cad435/OpenDALI_EVG/Hardware/DALI_Load_250W_RGBW/BOM-DALI_EVG_LoadBoard(V0.1).pdf

Comment | Description | Designator | Footprint | Quantity
MOC3043 | Zero-Cross Triac Driver Output Optocoupler | A1 | DIP762W46P254L889H5 08Q6B | 1
1uF/25V | Capacitor | C1, C2, C3, C8 | C0603 | 4
10uF/25V | Capacitor | C5, C6 | C0805 | 2
ACST410-8BTR | TRIAC Alternistor -Snubberless, 600V, 4A DPAK | D1 | TO229P994X240-3N (DPAK) | 1
BZT52C15S (15V) | Zener | D4 | SOD-323 | 1
1.5A | Fuse | F1 | 1808 Fuse / FUSE_0154004 | 1
FFC 0.5mm 10Pin 90° | FFC 0.5mm 10P Bottom Connection C262659 | J1 | TE_1-1734592-0 | 1
KF142R-5.08-4P | KF142R-5.08-4P | P1 | CONN-TH_4P-P5.08_KF142R-5.08-4P | 1
KF2EDGR-3.81-5Pin | KF2EDGR-3.81-5Pin | P2 | CONN-TH_5P-P3.81_KF2EDGR-3.81-5P | 1
4 Pin male | 4 Pin male | P7 | TE_826647-4 | 1
MMBT5551 | NPN General Purpose Transistor | Q2 | SOT23 | 1
IRLU024N | N-HEXFET Power MOSFET | Q3, Q4, Q5, Q6 | TO228P680X240X837-3 (TO-251) | 4
10 | Resistor | R1, R2, R3, R7, R8, R9, R10, R17 | R0603 | 8
390 | Resistor | R4, R16 | R1206 | 2
22k | Resistor | R5 | R0603 | 1
0 | Resistor | R6 | R1206 | 1
100k | Resistor | R11, R12, R13, R14, R15 | R0603 | 5
UCC27517DBVR | 4-A/4-A single-channel gate driver with 5-V UVLO and 13-ns prop delay in SOT-23 package | U1, U2, U3, U4 | SOT23-5 | 4
