cad435/OpenDALI_EVG/Hardware/DALI_Load_250W_RGBW/DALI_EVG_LoadBoard_V0.1-Schematic.PDF

J1

P2

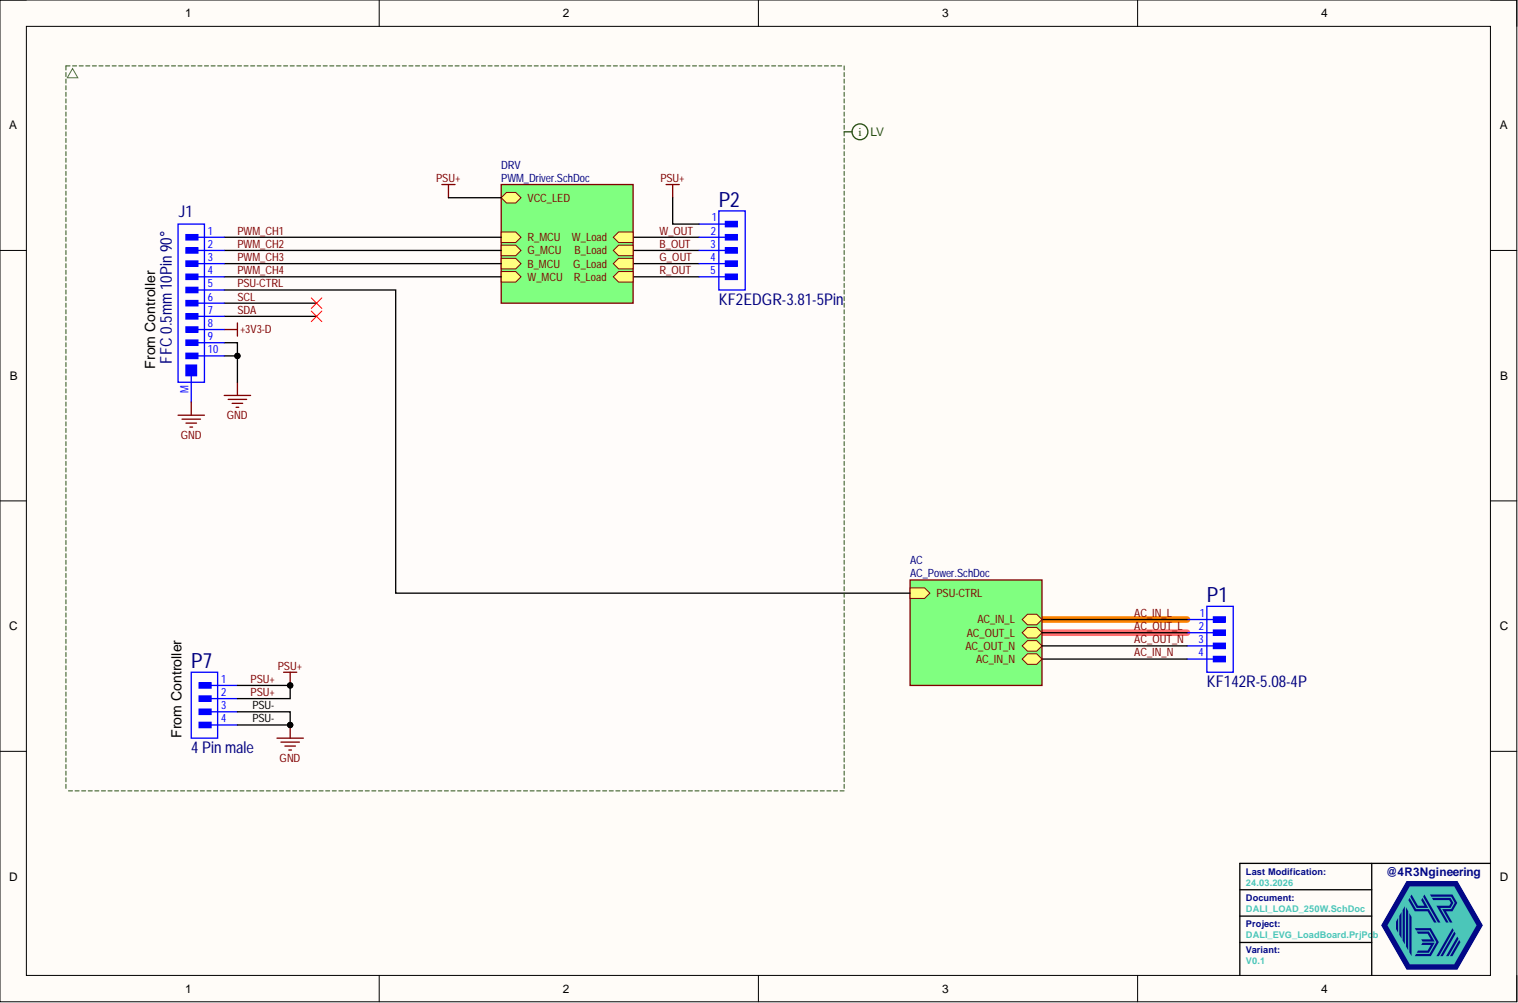
[picture p31: page 1]
st Modific; ation:; Docum; ent: DALI_LOAD_; W.SchDoc; Proje; ct: DALI_EVG; _LoadBoard.PrjPc; ariant: V0.1; PSU; 4 Pin male; R_Load; B_Load G_Load; W_Load; C_LED; V PWM_Dri; ver.SchDoc; - PSU; PWM_C; PSU-CTR; SDA +3V3-D; From Controller; AC AC_Power.SchDoc; FFC 0.5mm 10Pin 90°; KF2EDGR-3.81-5Pin

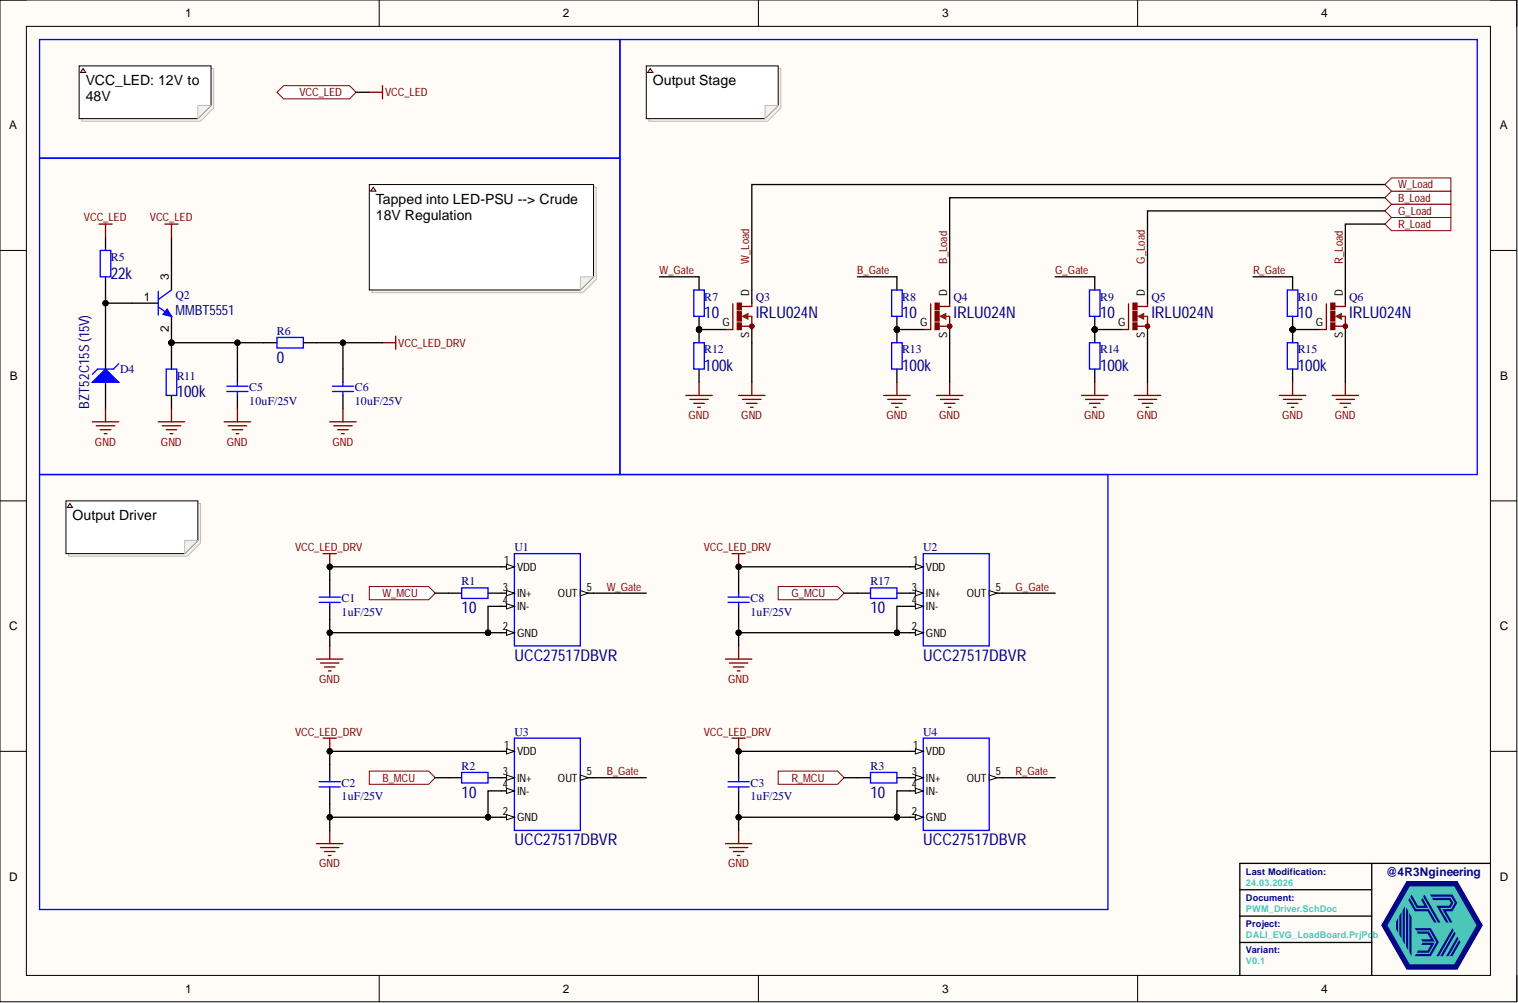
[picture p32: page 2]

Tapped into LED-PSU --> Crude
18V Regulation

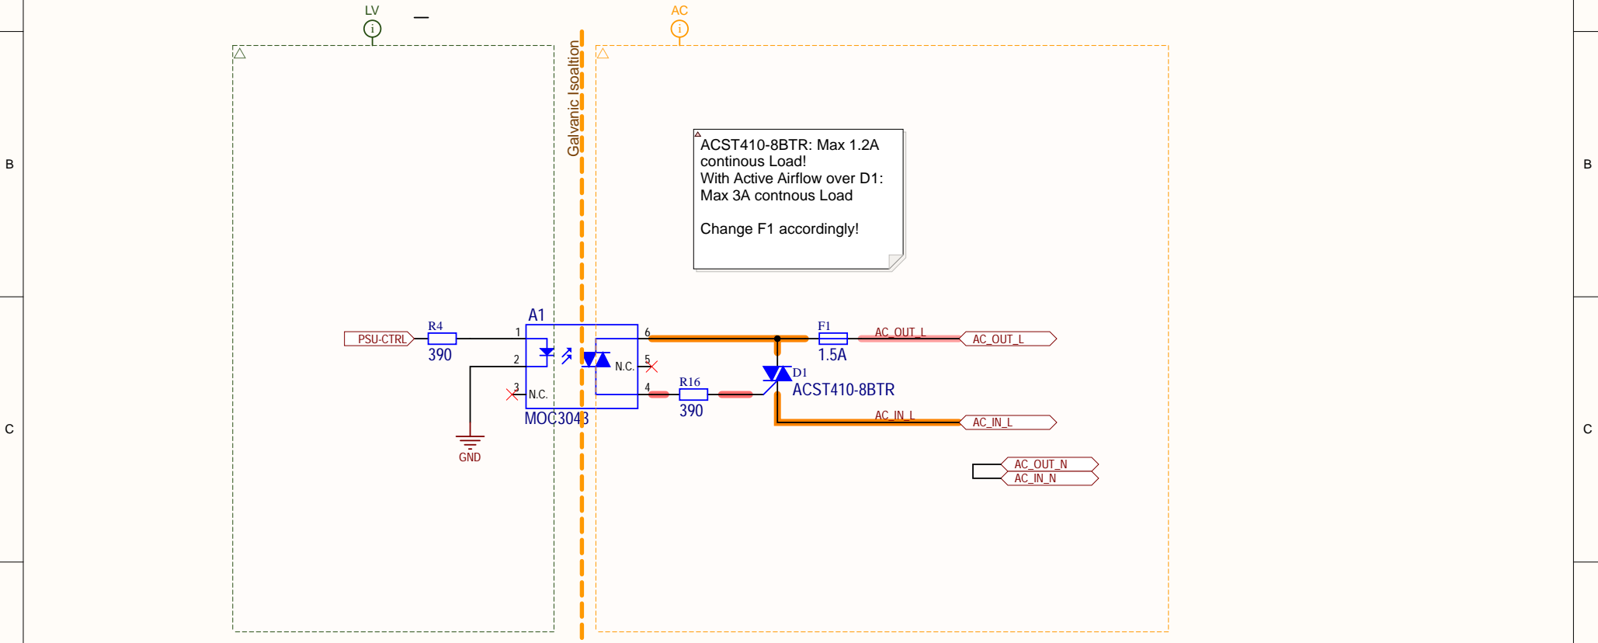
[picture p33: figure]
AC_OUT_L; AC_OUT_N AC_IN_N; MOC3043; PSU-CTRL; GND; Galvanic Isoaltion; D1 ACST410-8BTR; ACST410-8BTR: Max 1.2A continous Load! With Active Airflow over D1: Max 3A contnous Load; Change F1 accordingly!

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
D | D
A | A
Last Modification: | @4R3Ngineering 24.03.2026

Document:
AC_Power.SchDoc

Project:
DALI_EVG_LoadBoard.PrjPcb

Variant:
