cad435/OpenDALI_EVG/Hardware/DALI_Load_250W_RGBW/DALI_EVG_LoadBoard_V0.1_Assembly.PDF

A

B

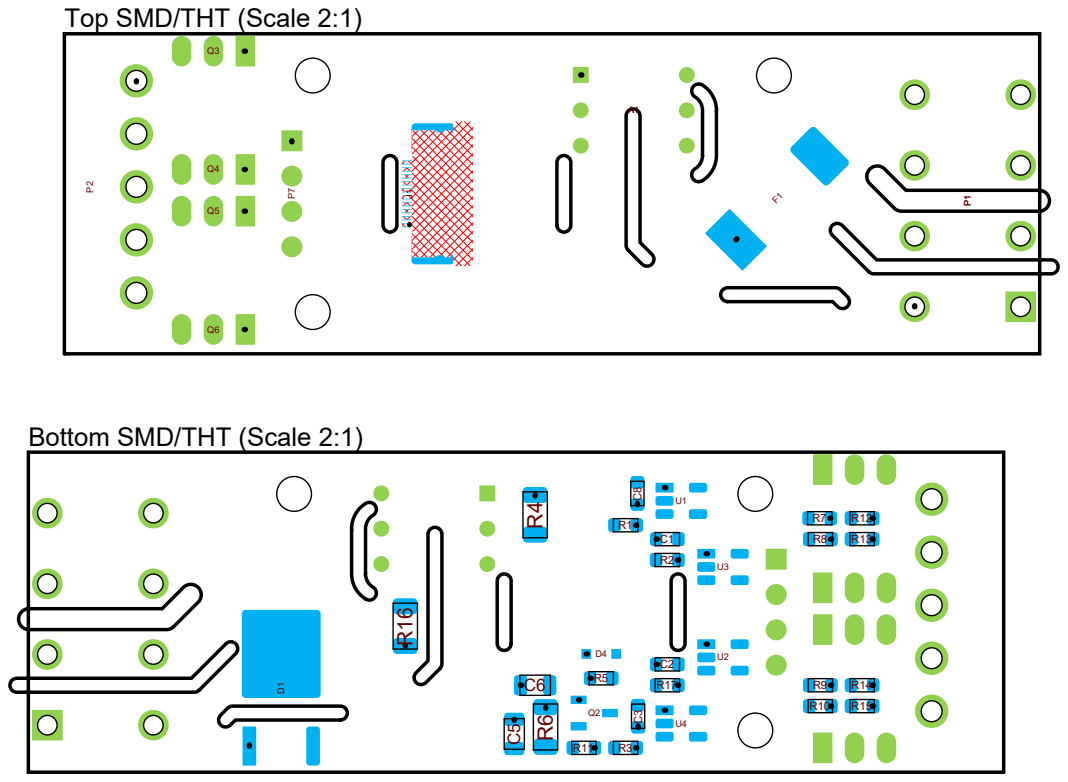
[picture p34: page 1]

Top SMD/THT (Scale 2:1) D¹

Bottom SMD/THT (Scale 2:1)

1 | 1

# Top SMD (Scale 2:1)

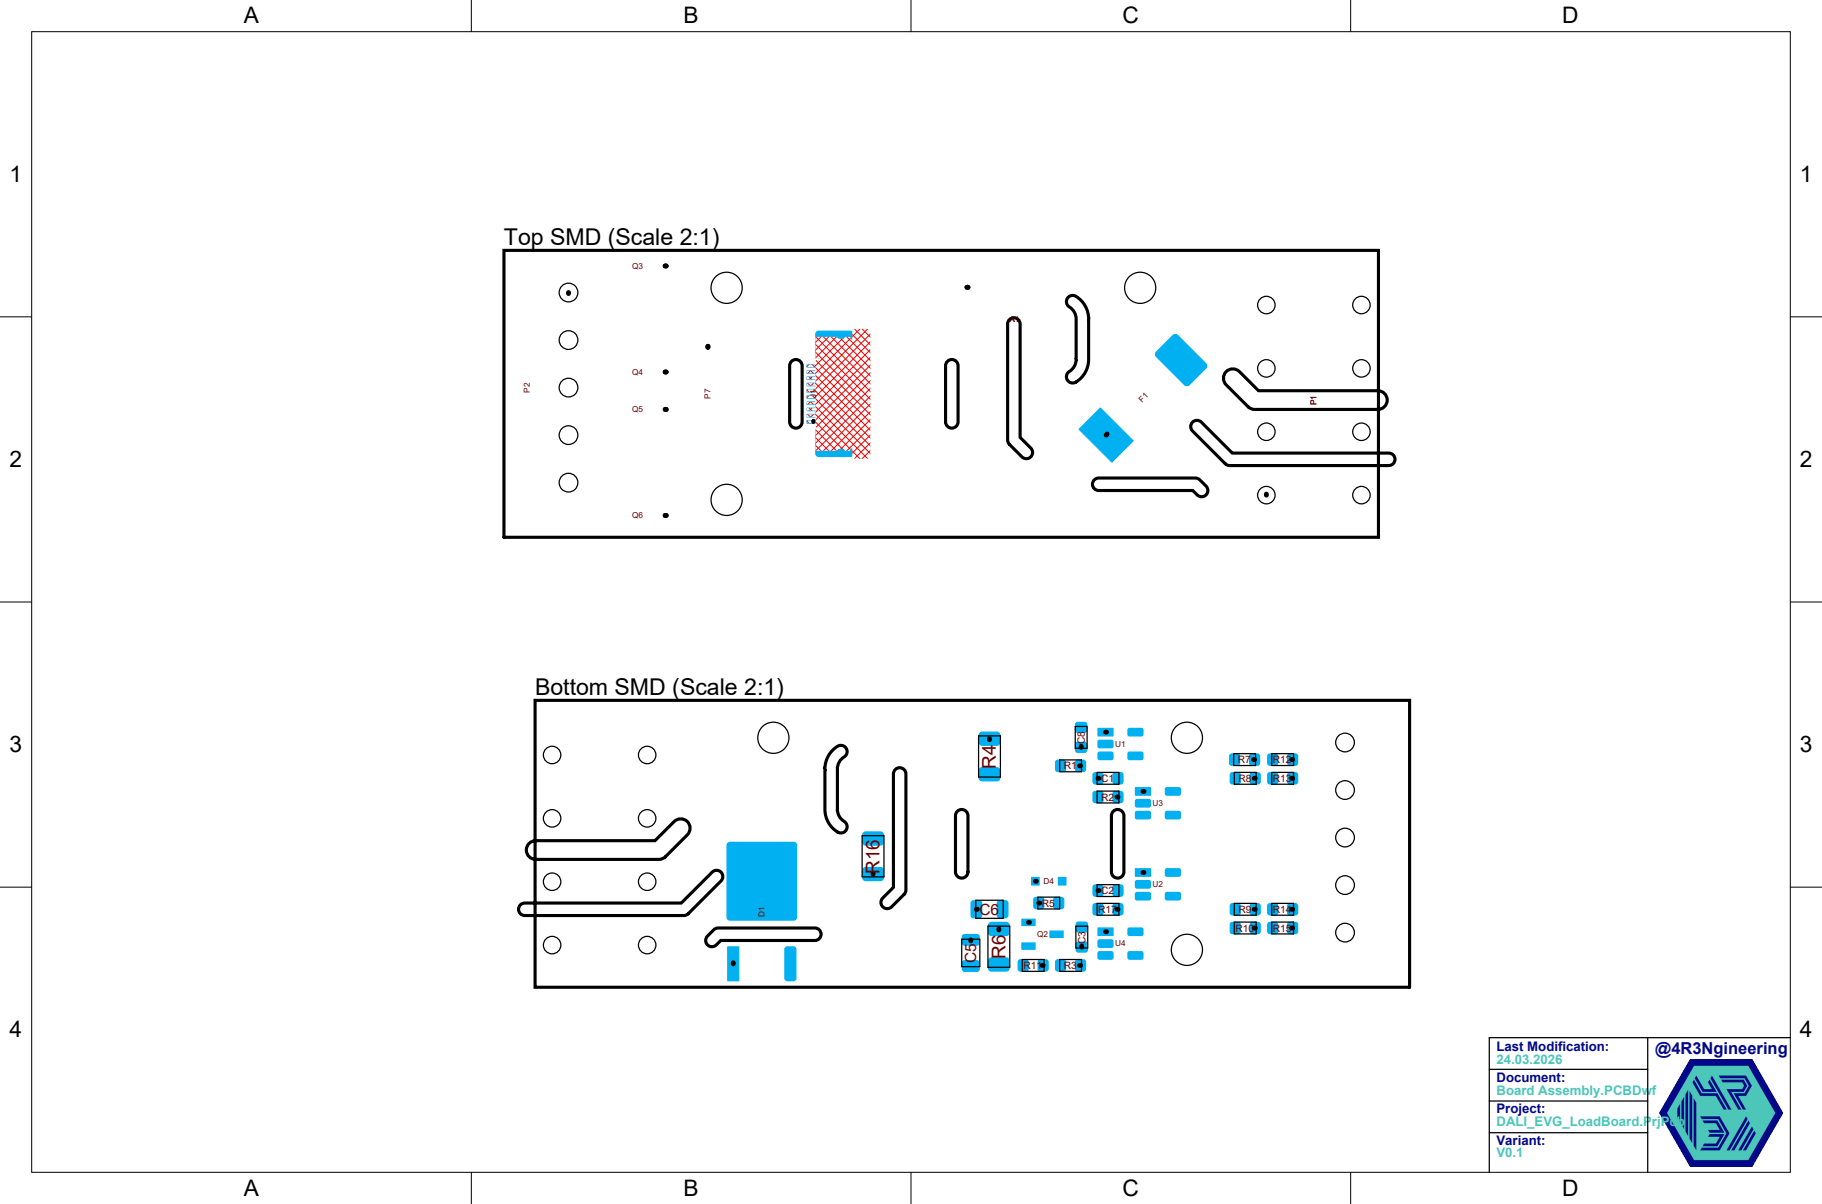
[picture p35: page 2]

1 | 1

# Top THT (Scale 2:1)

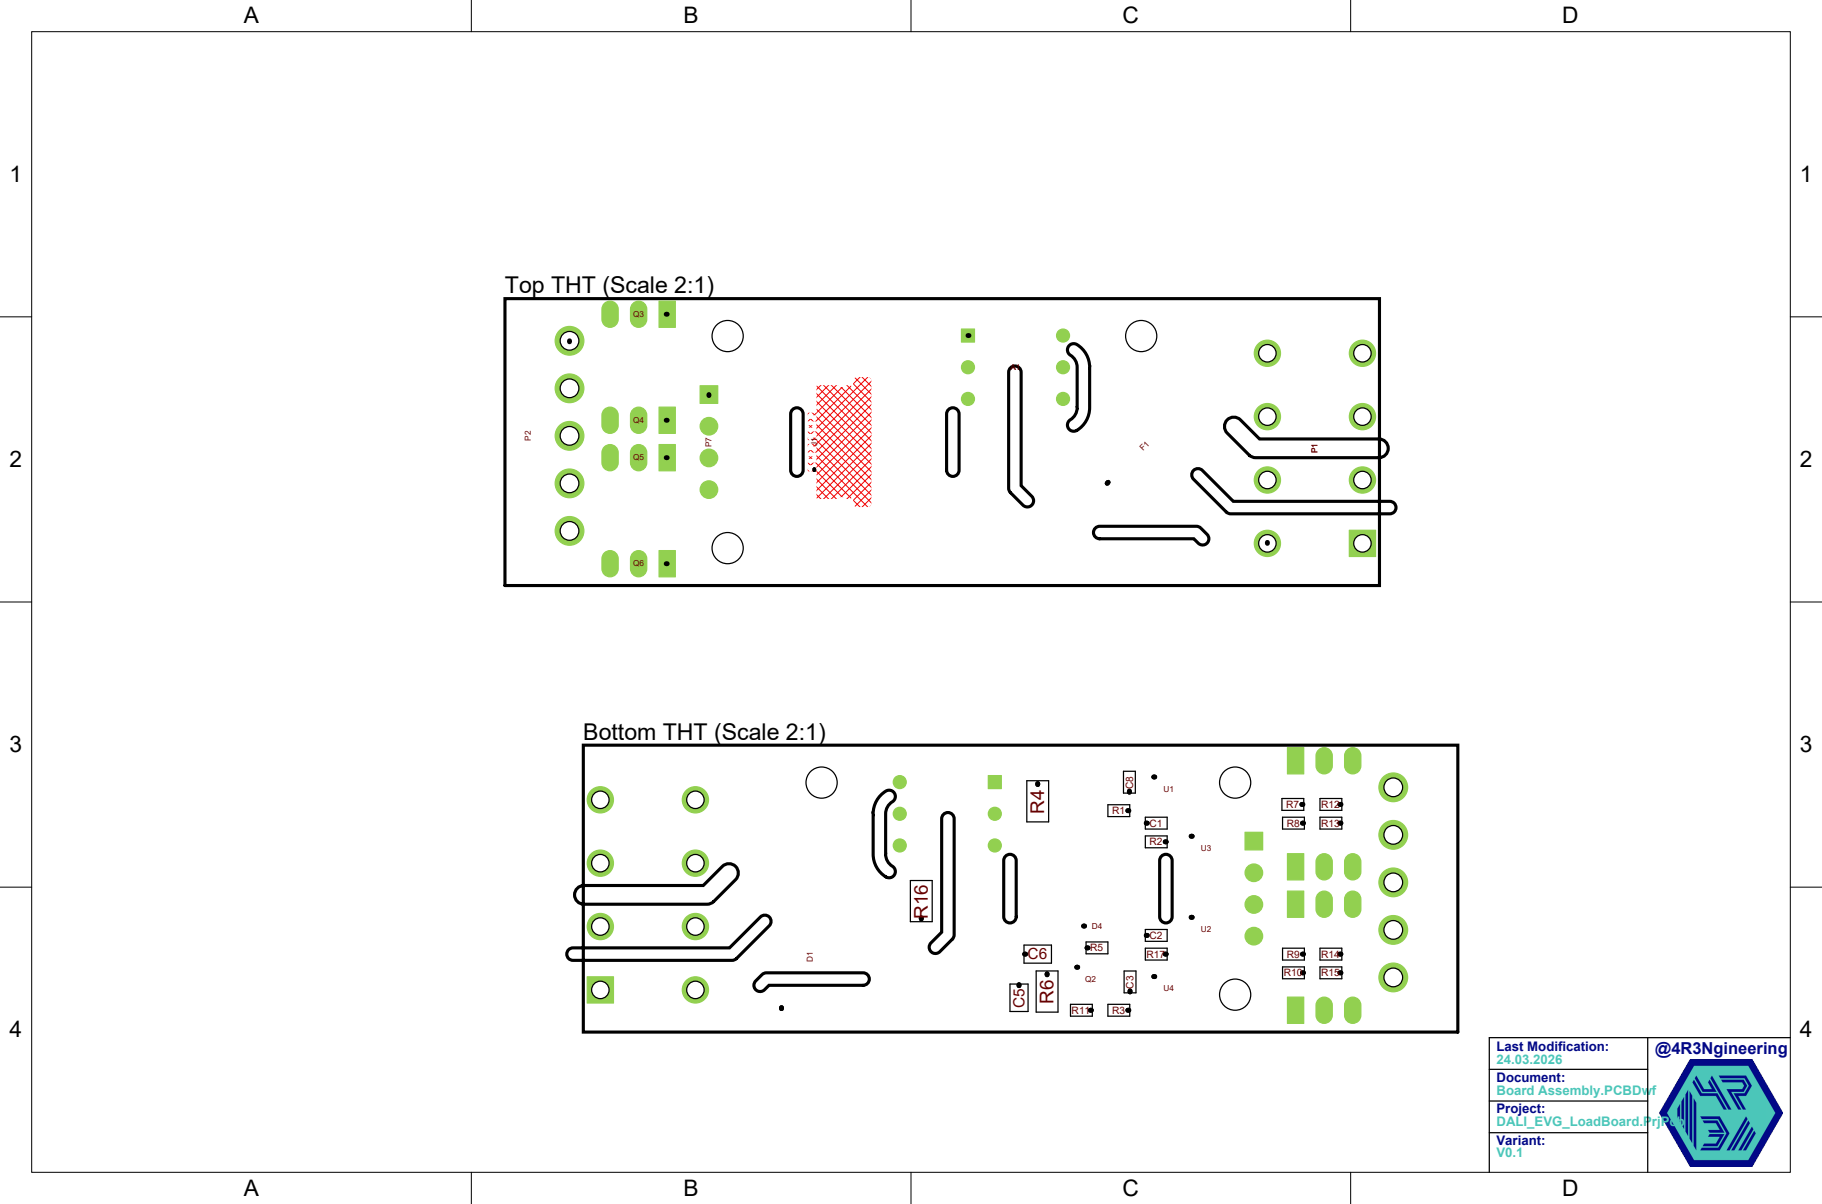
[picture p36: page 3]

1 | 1
2 | 2

# Realistic View

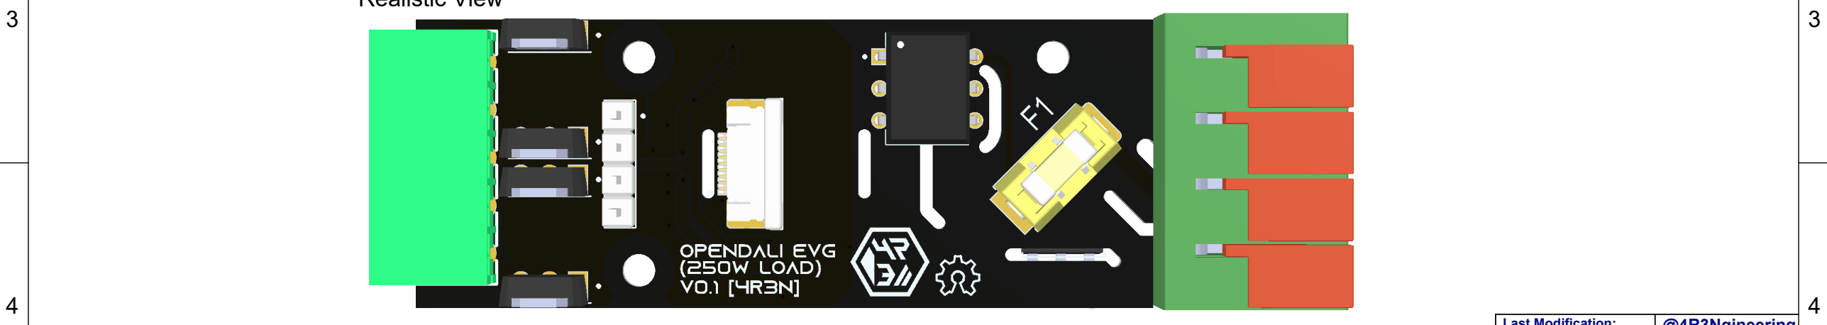
[picture p37: figure]

Last Modification: | @4R3Ngineering
24.03.2026
Document:
Board Assembly.PCBDwf
