cad435/OpenDALI_EVG/Hardware/DALI_Load_250W_RGBW/DALI_EVG_V0.1-Schematic.PDF

# ver.SchDoc ¹²

## LED DC

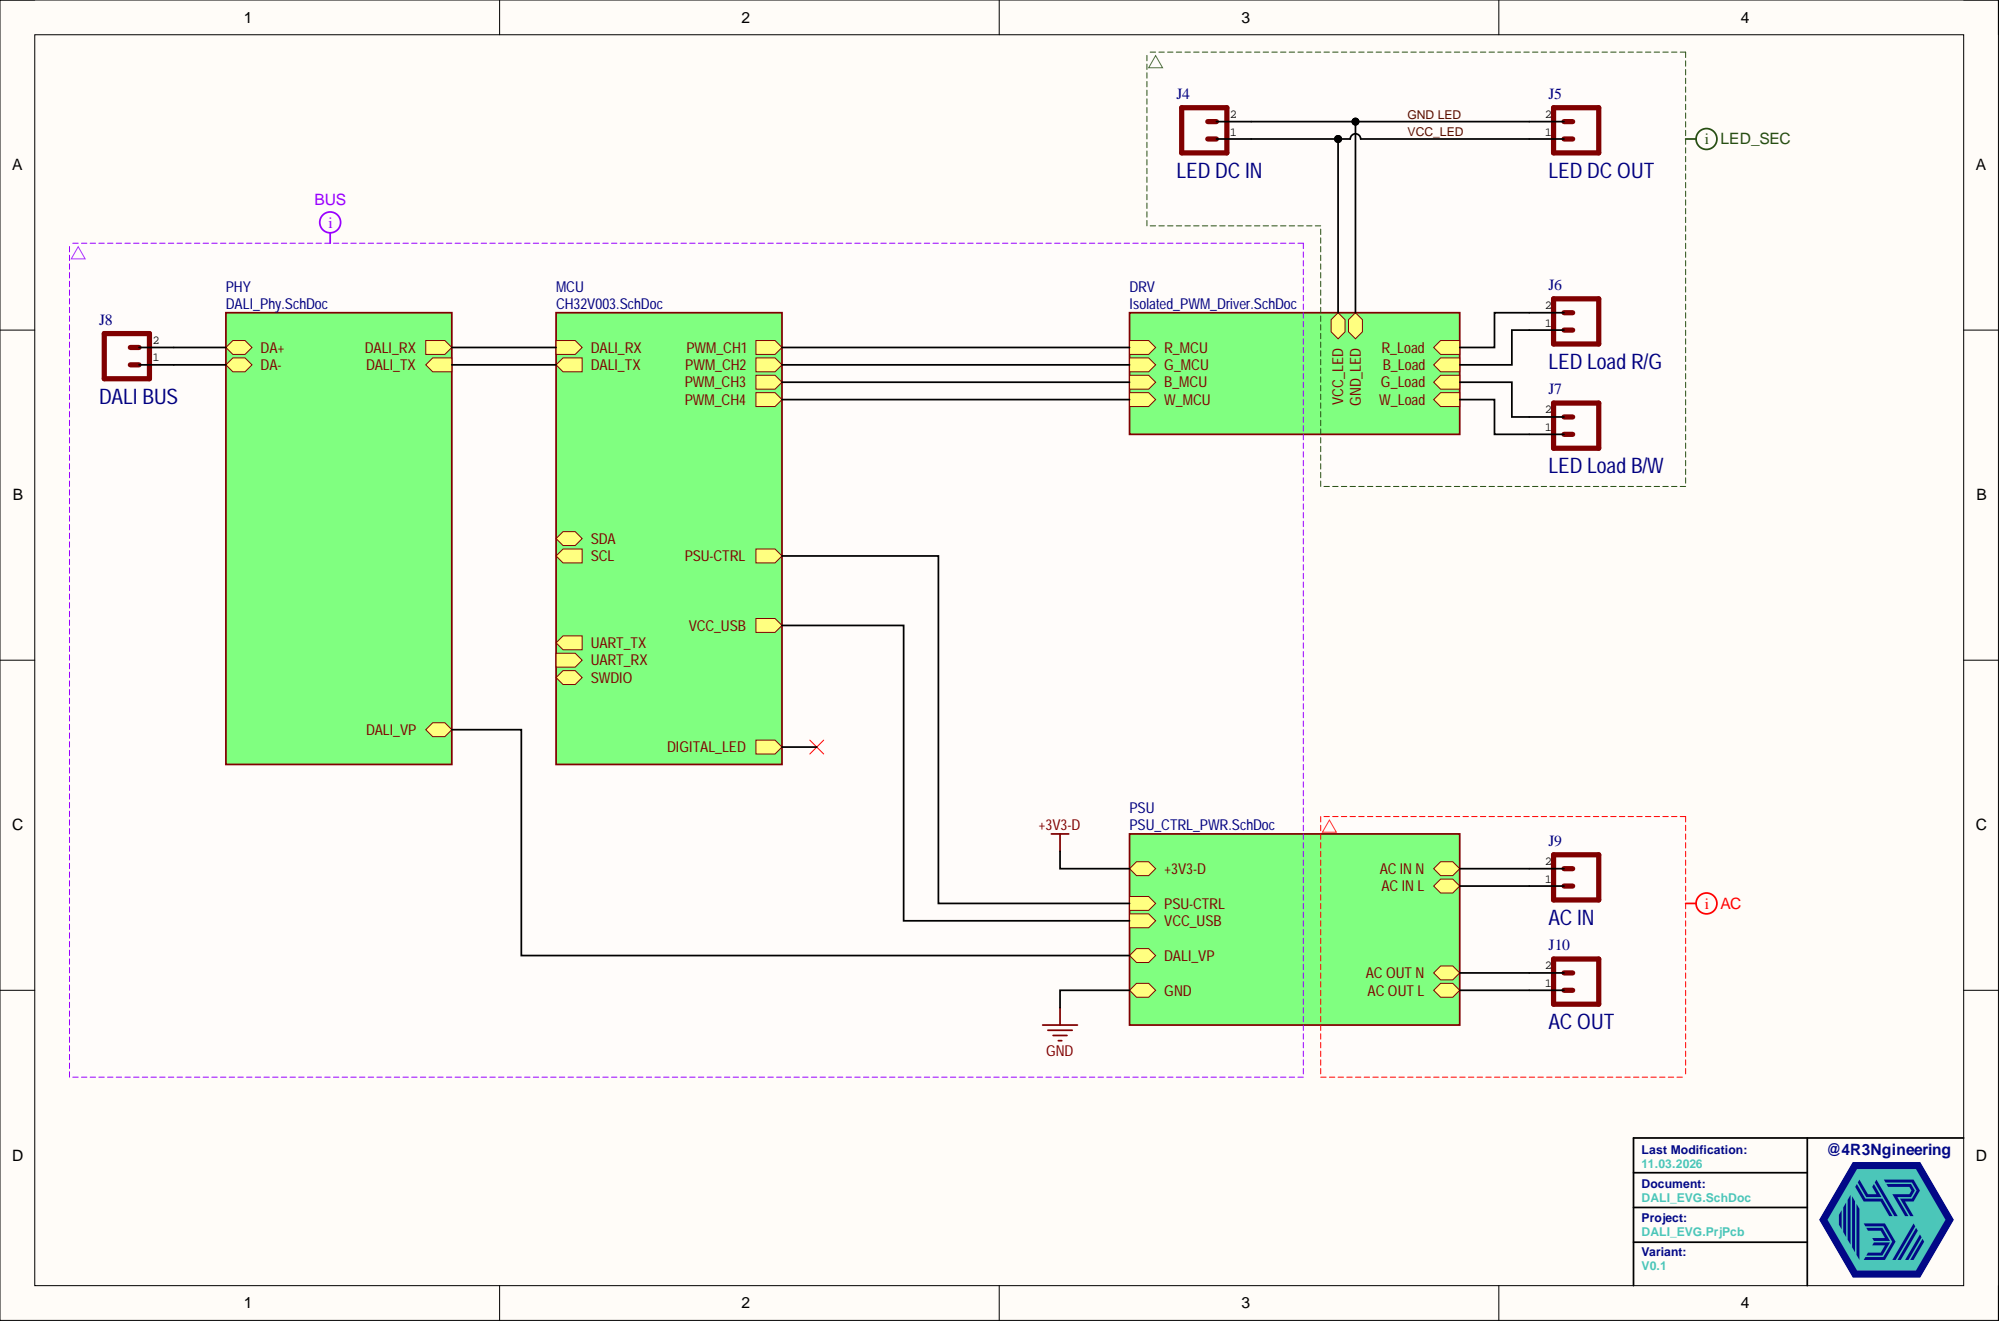
[picture p38: page 1]
st Modific; ation:; Docum; ent: DALI_EVG.SchDoc; Proje; ct: DALI_EVG.PrjPc; ariant: V0.1; PWM_C; PSU-CTR; DALI_RX; SDA SCL; H3 PWM_C; DALI_TX; UART_TX UART_RX; SWDIO; VCC_USB; DIGITAL_LED; MCU CH32V003.SchDoc; DALI_RX DALI_TX; DALI_VP; PHY DALI_Phy.SchDoc; AC OUT N AC OUT L; VCC_USB DALI_VP +3V3-D GND; PSU; PSU_CTRL_PWR.SchDoc R_MCU G_MCU; B_MCU W_MCU; R_Load B_Load G_Load; W_Load; LED; GND; DRV Isolated_PWM_Dri; LED DC; OUT; LED Load R/G 12J7 LED Load B/W 12J9; i LED_S E; DALI BUS; GND LED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

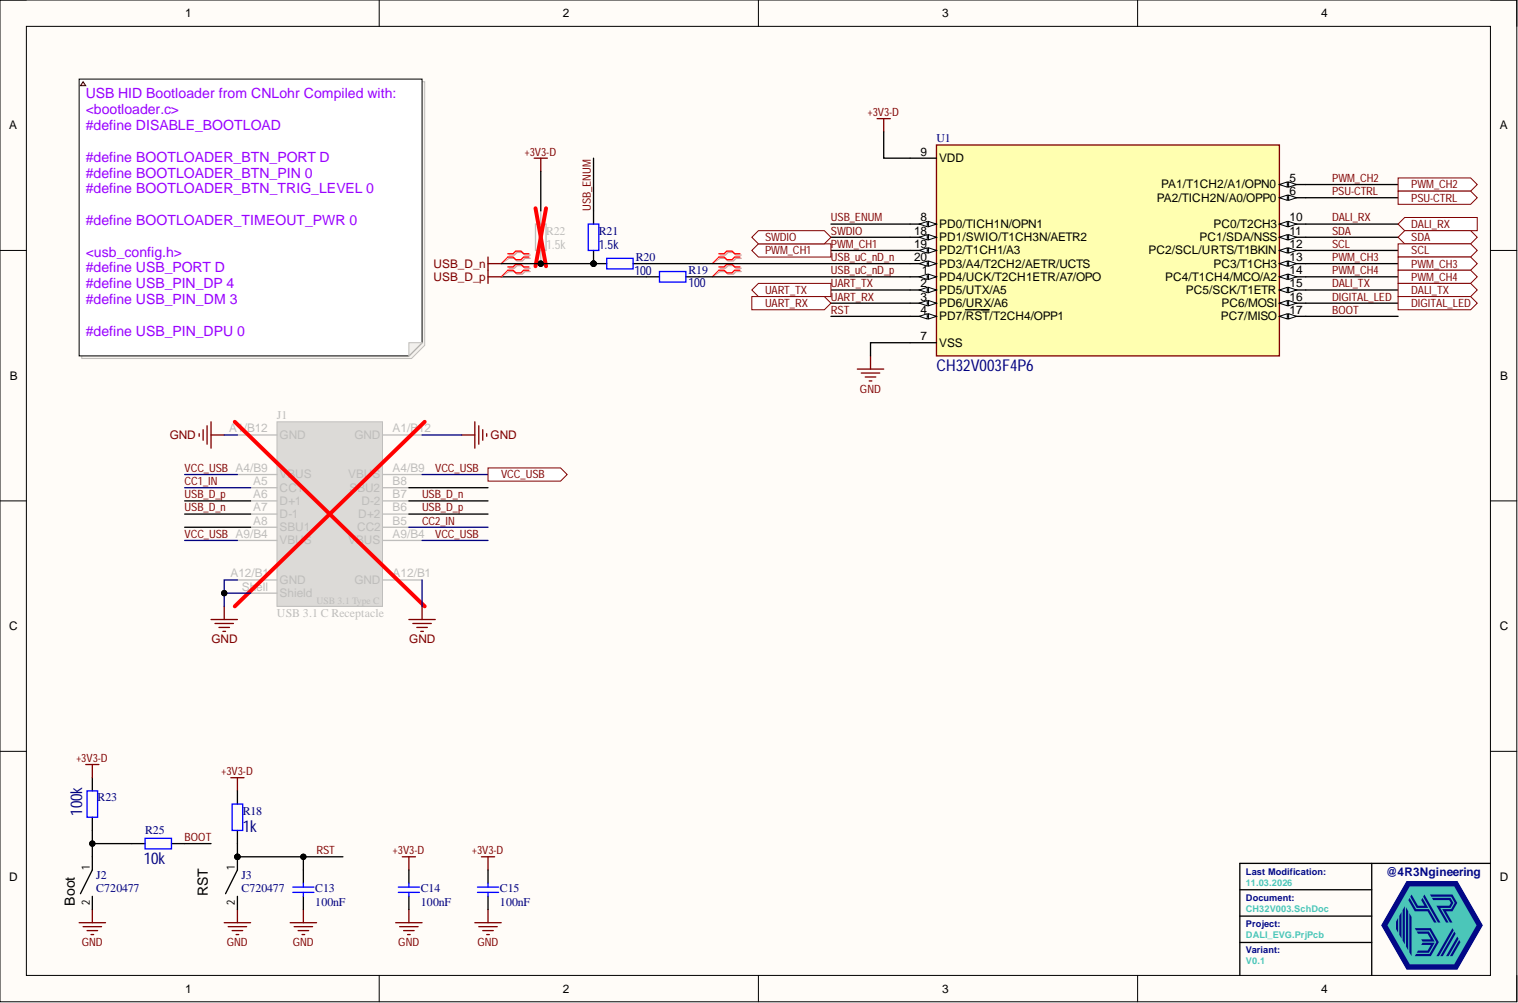
[picture p39: page 2]

USB HID Bootloader from CNLohr Compiled with:
<bootloader.c>
#define DISABLE_BOOTLOAD

D3

## MB10S

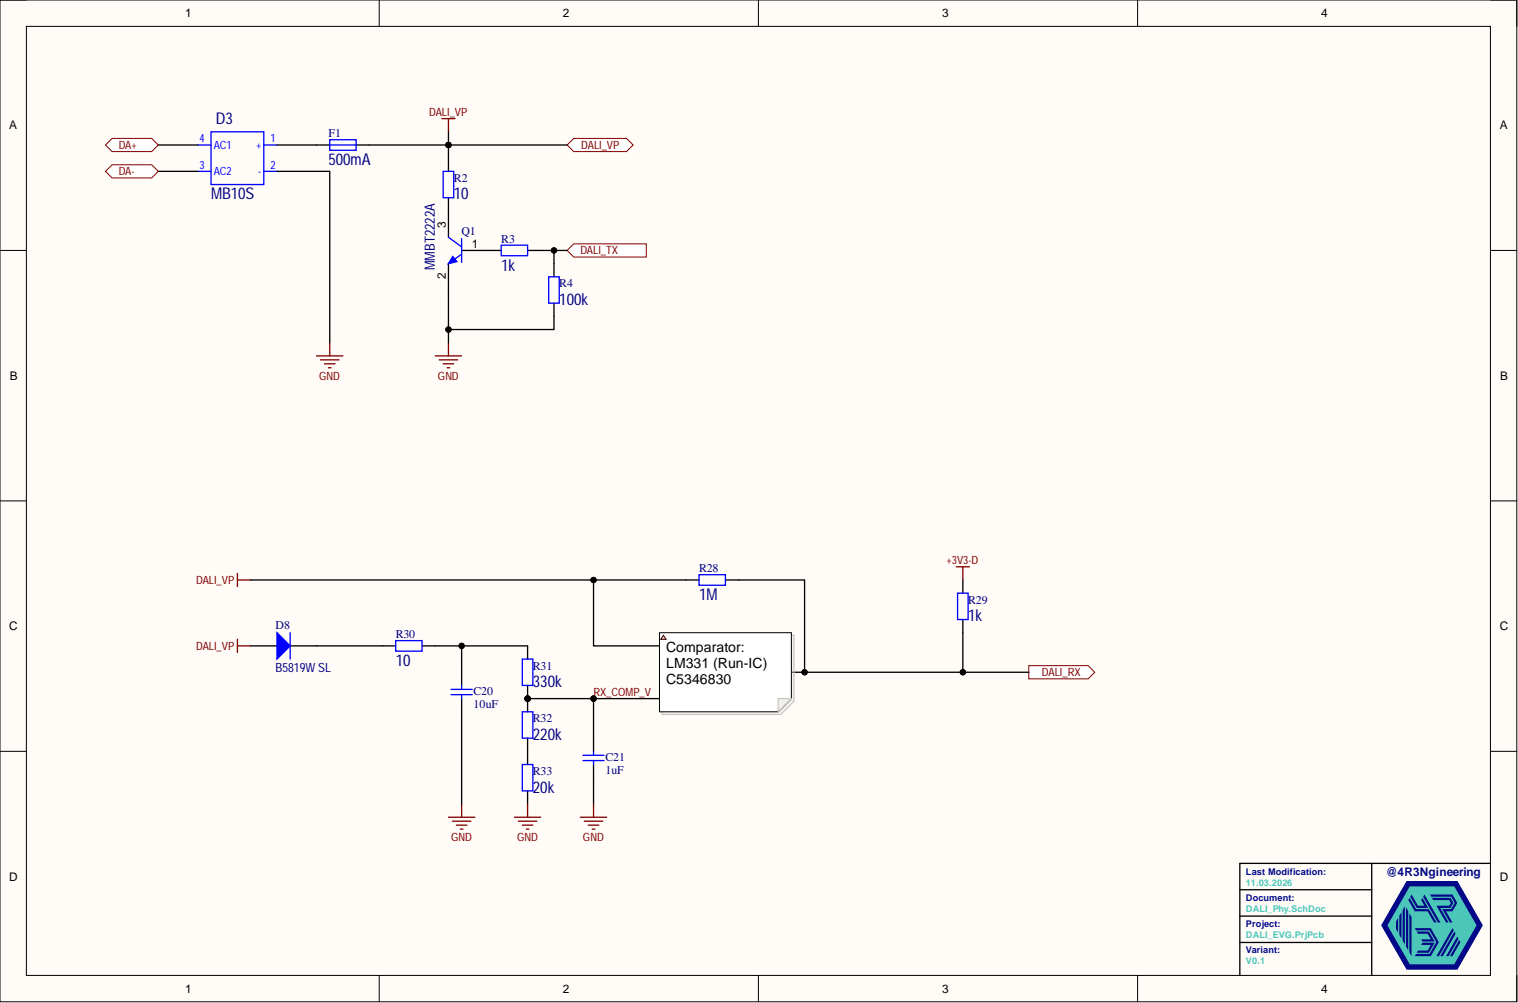
[picture p40: page 3]

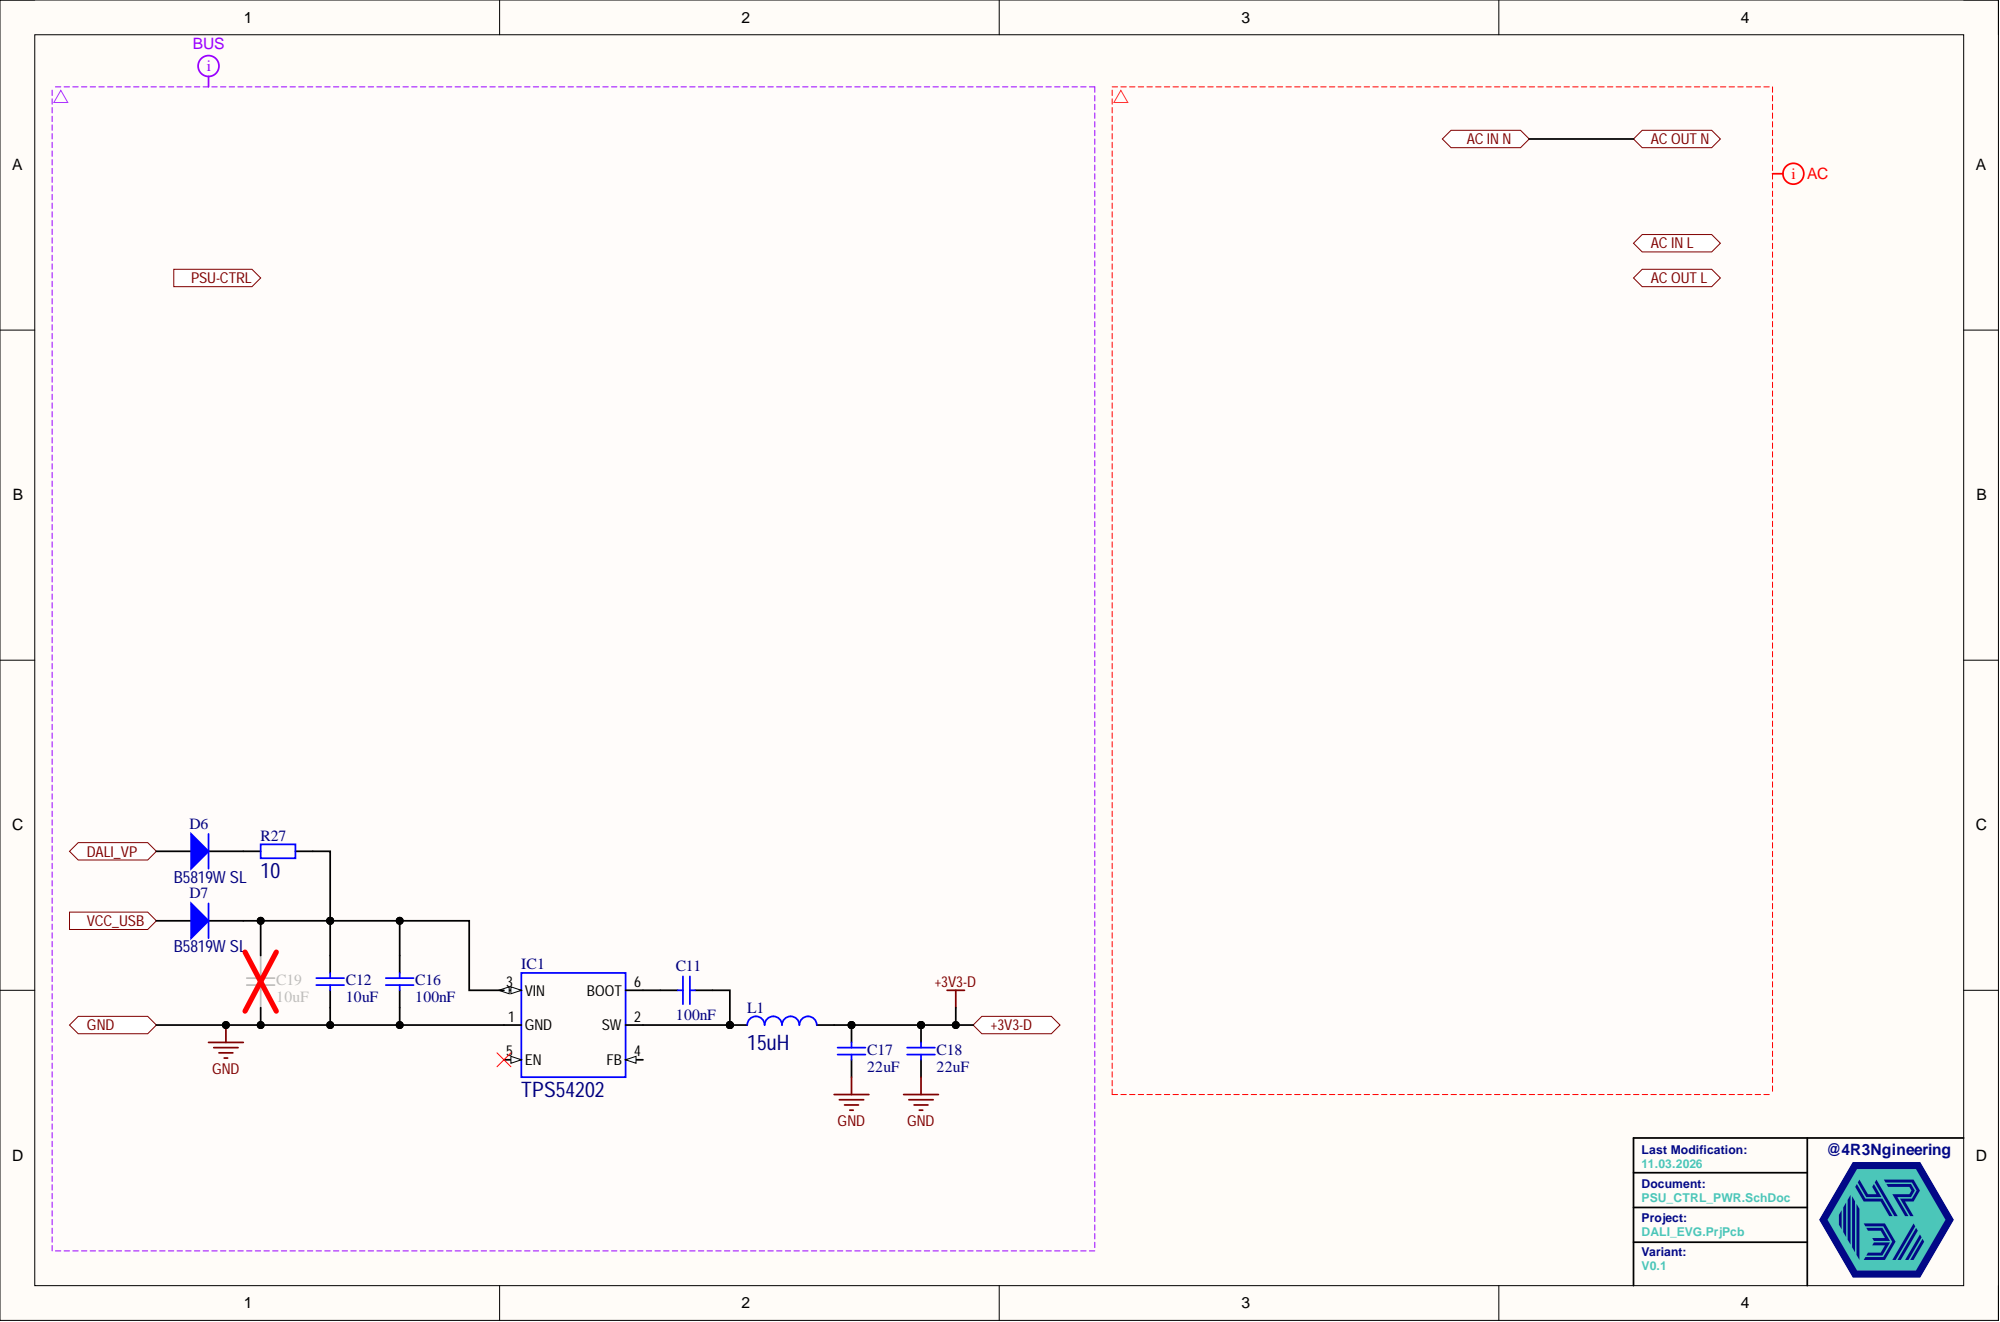
[picture p41: page 4]

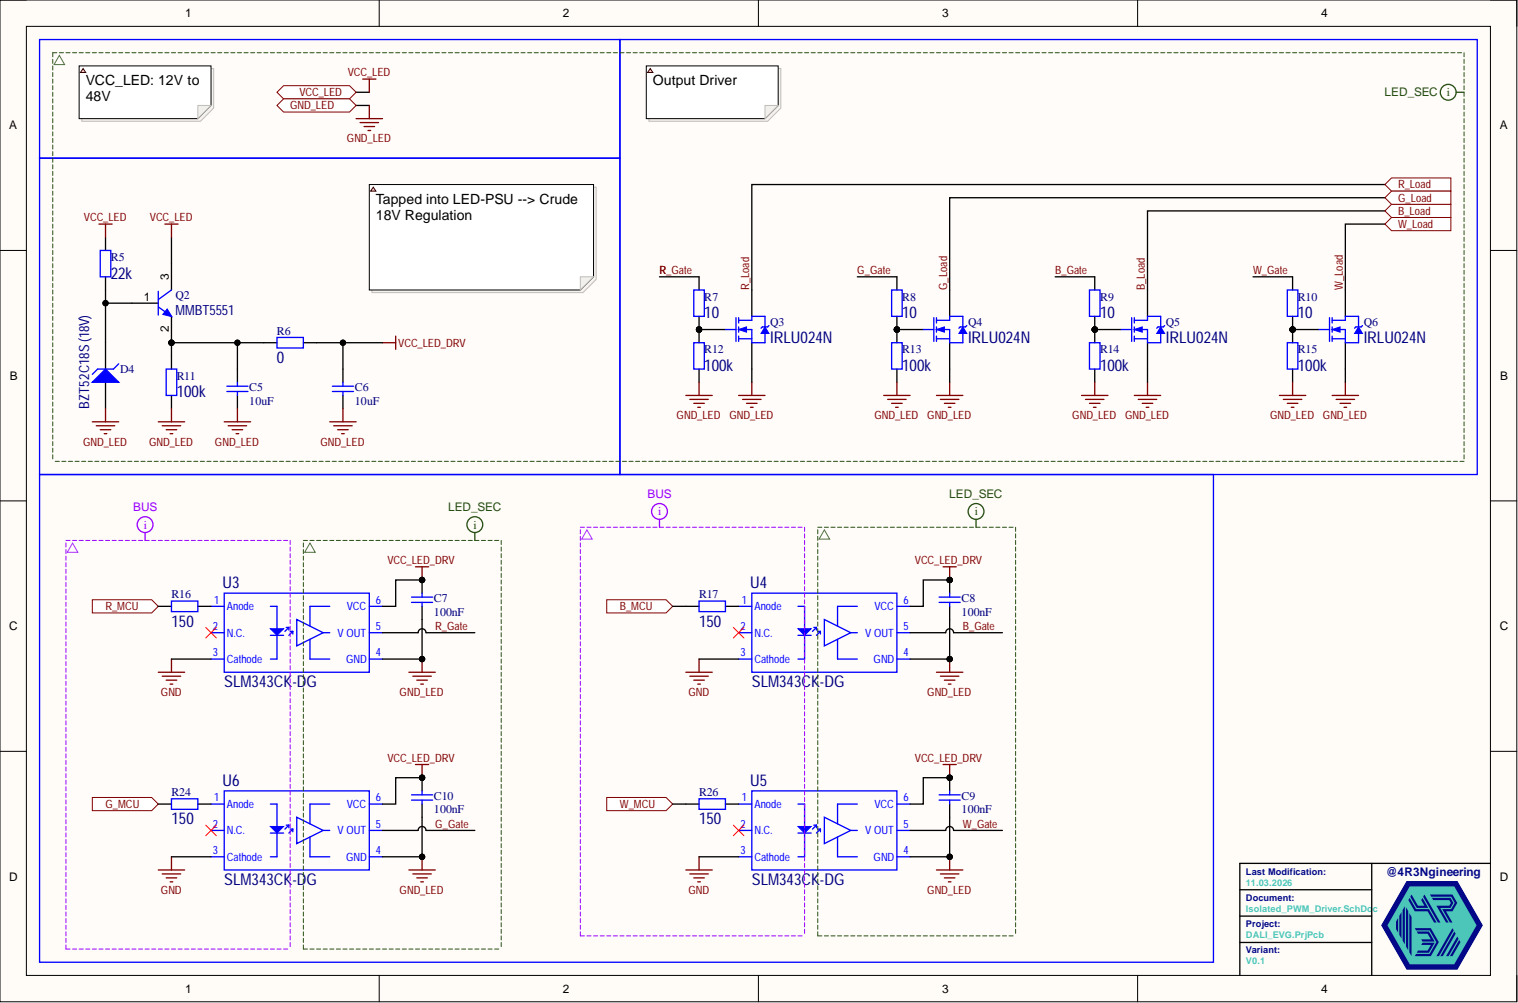
[picture p42: page 5]

Tapped into LED-PSU --> Crude
18V Regulation
