cad435/OpenDALI_EVG/Hardware/Controller/DALI_EVG_Controller_V0.1-Schematic.PDF

P7

## Header

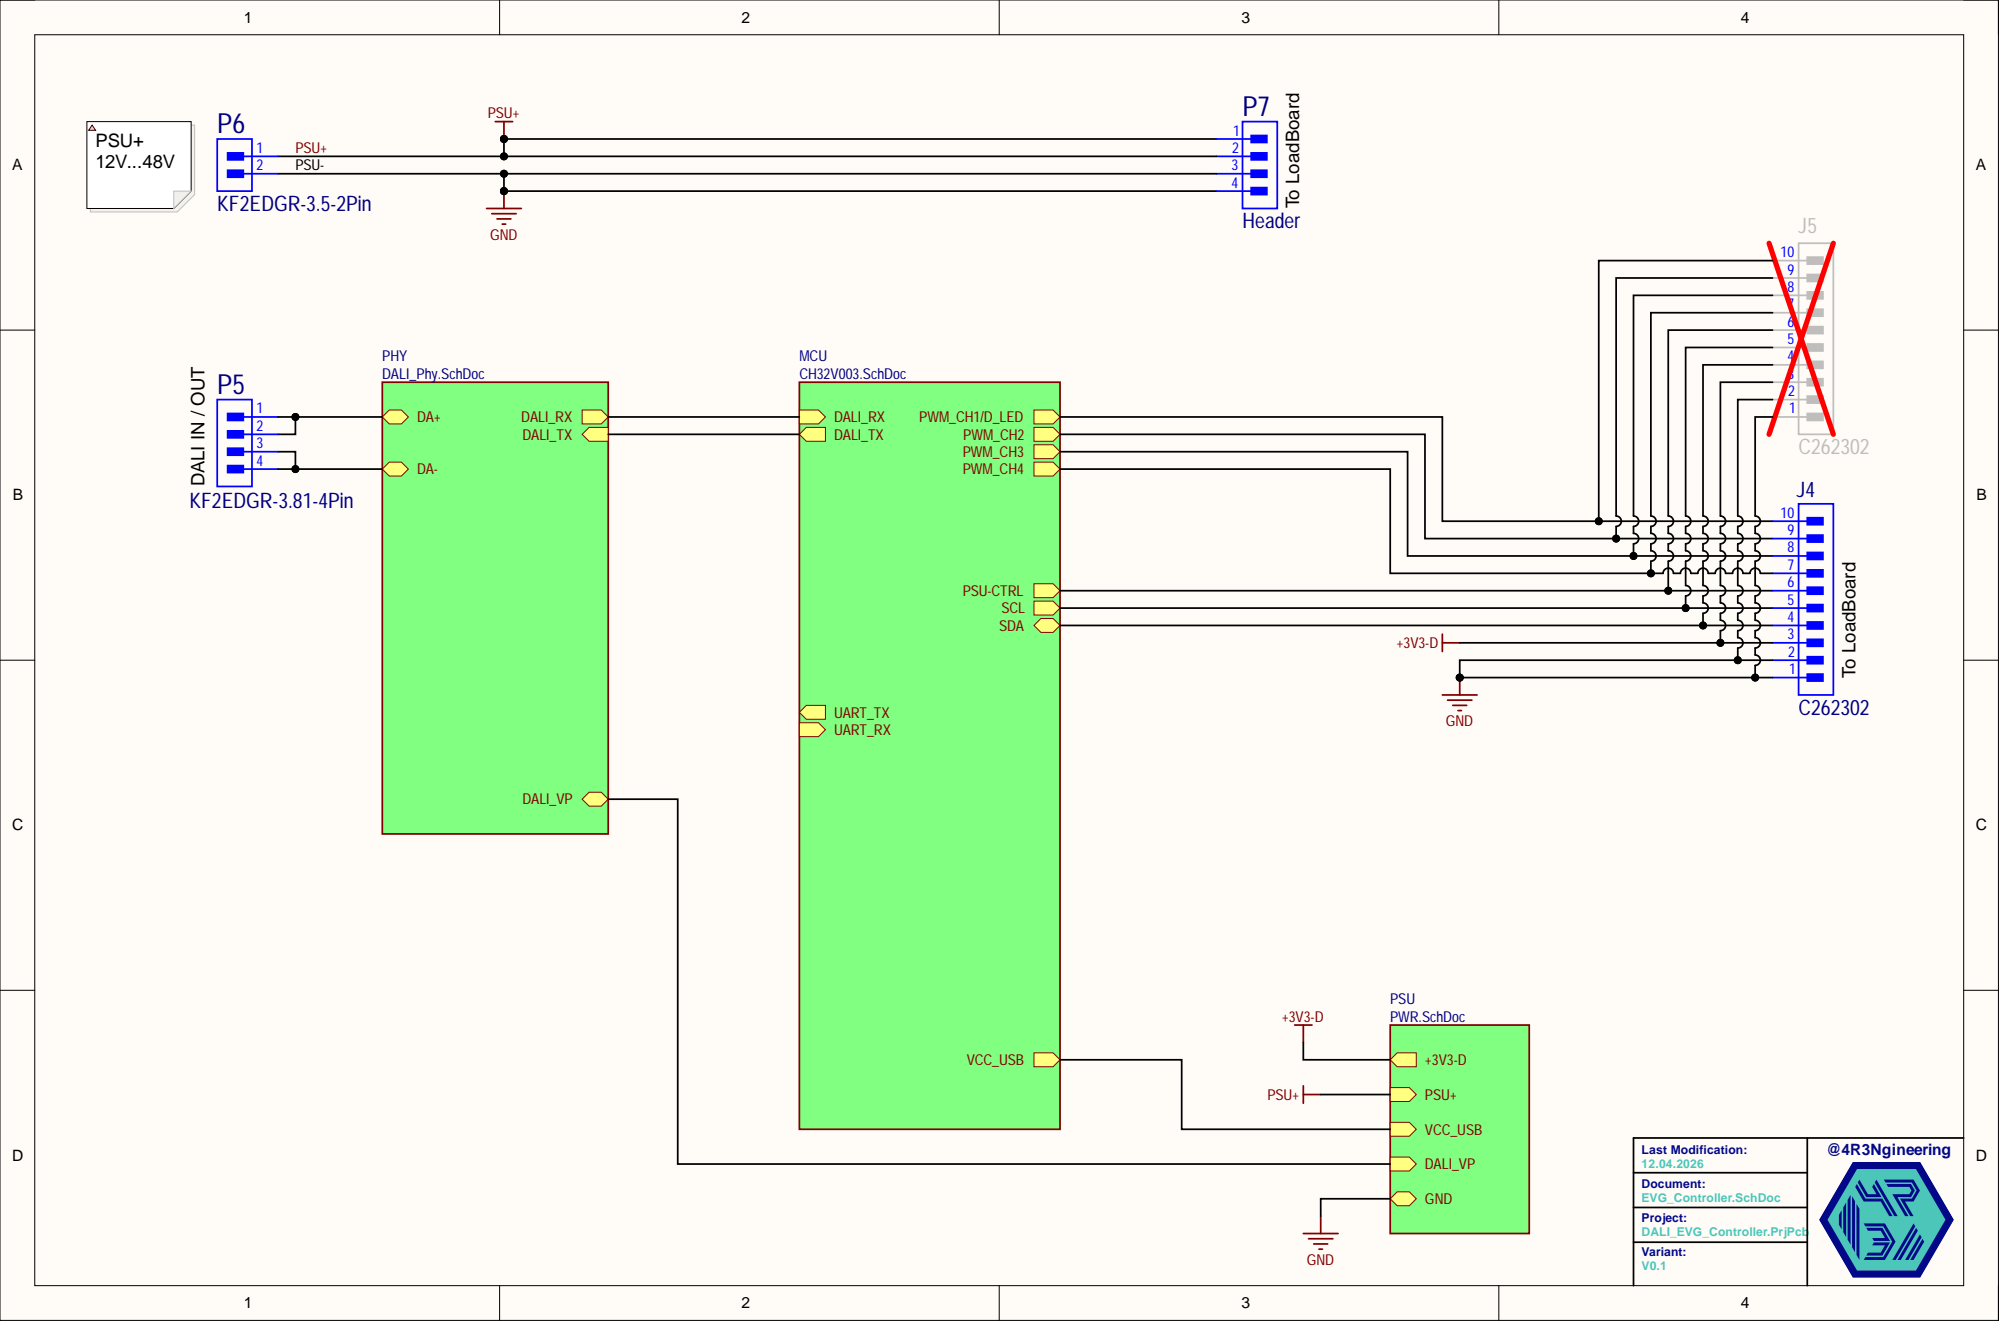
[picture p57: page 1]
st Modific; ation:; Docum; ent:; EVG; _Controlle; r.SchDoc; Proje; ct: DALI_EVG; r.PrjPc; ariant: V0.1; PWM_C; PSU-CTR; DALI_R; SDA; DALI_TX; H1/D_LED; UART_TX UART_RX; C_USB; H32V003.SchDoc; X DALI_TX; DALI_VP; PHY DALI_Phy.SchDoc; DALI_VP +3V3-D GND; PSU; PSU PWR.SchDoc; To LoadBoard; KF2EDGR-3.81-4Pin; KF2EDGR-3.5-2Pin

DALI IN / OUT

# PD6 20 PD5 19 PD4 18 PD3 17 PD2 16 PD1 15

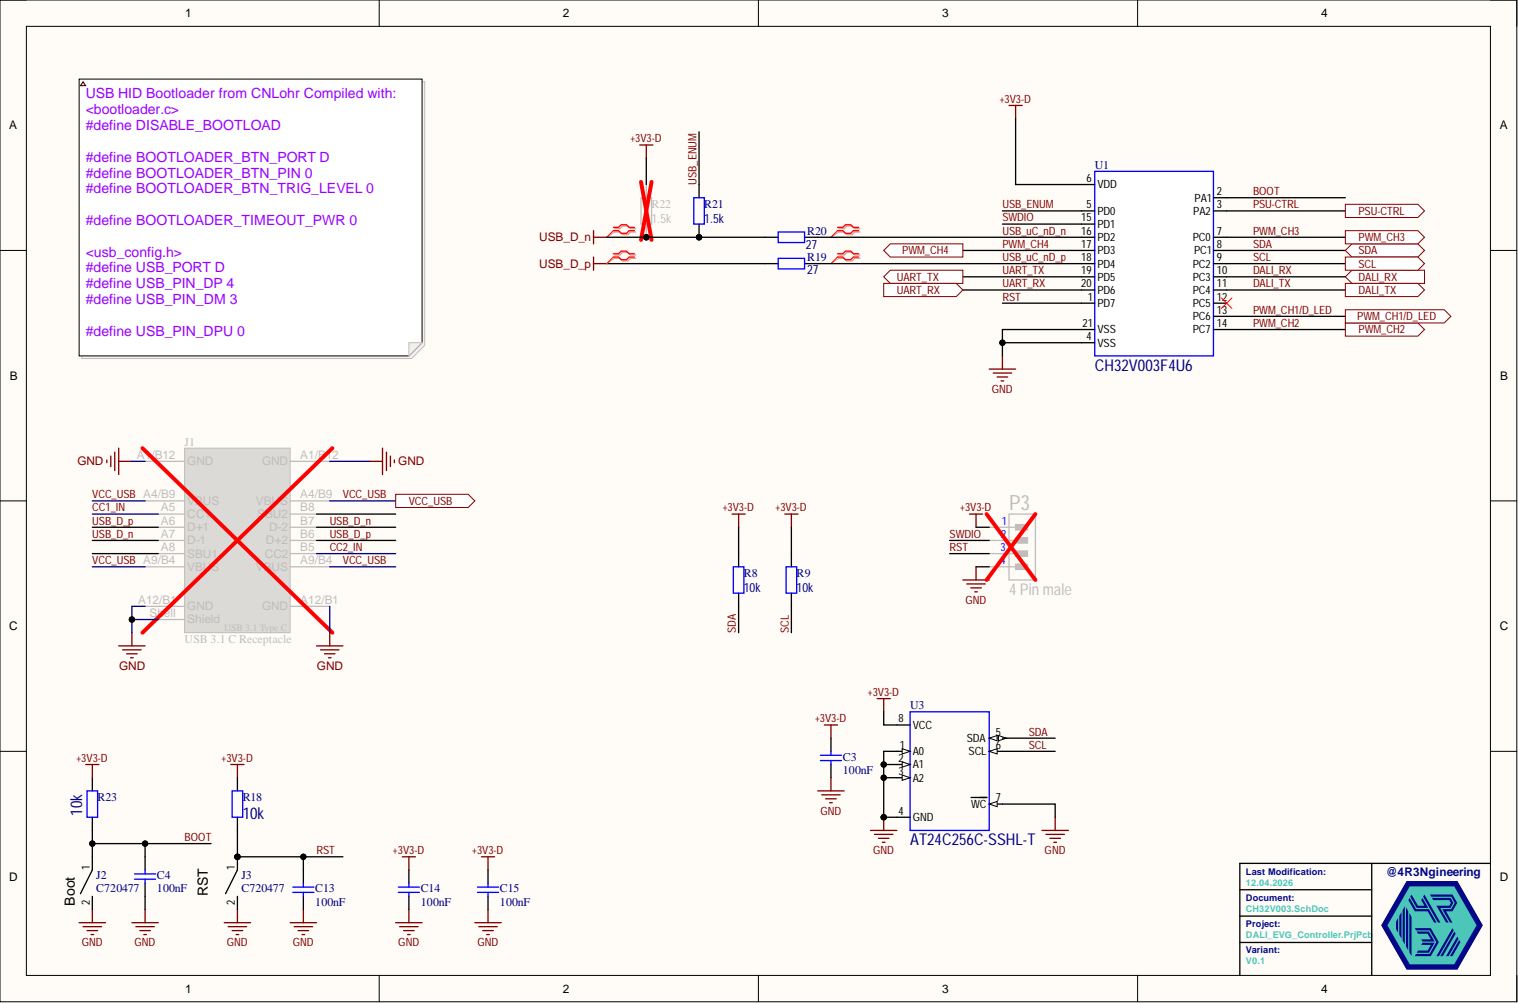
[picture p58: page 2]

USB HID Bootloader from CNLohr Compiled with:
<bootloader.c>
#define DISABLE_BOOTLOAD

D3

## MB10S

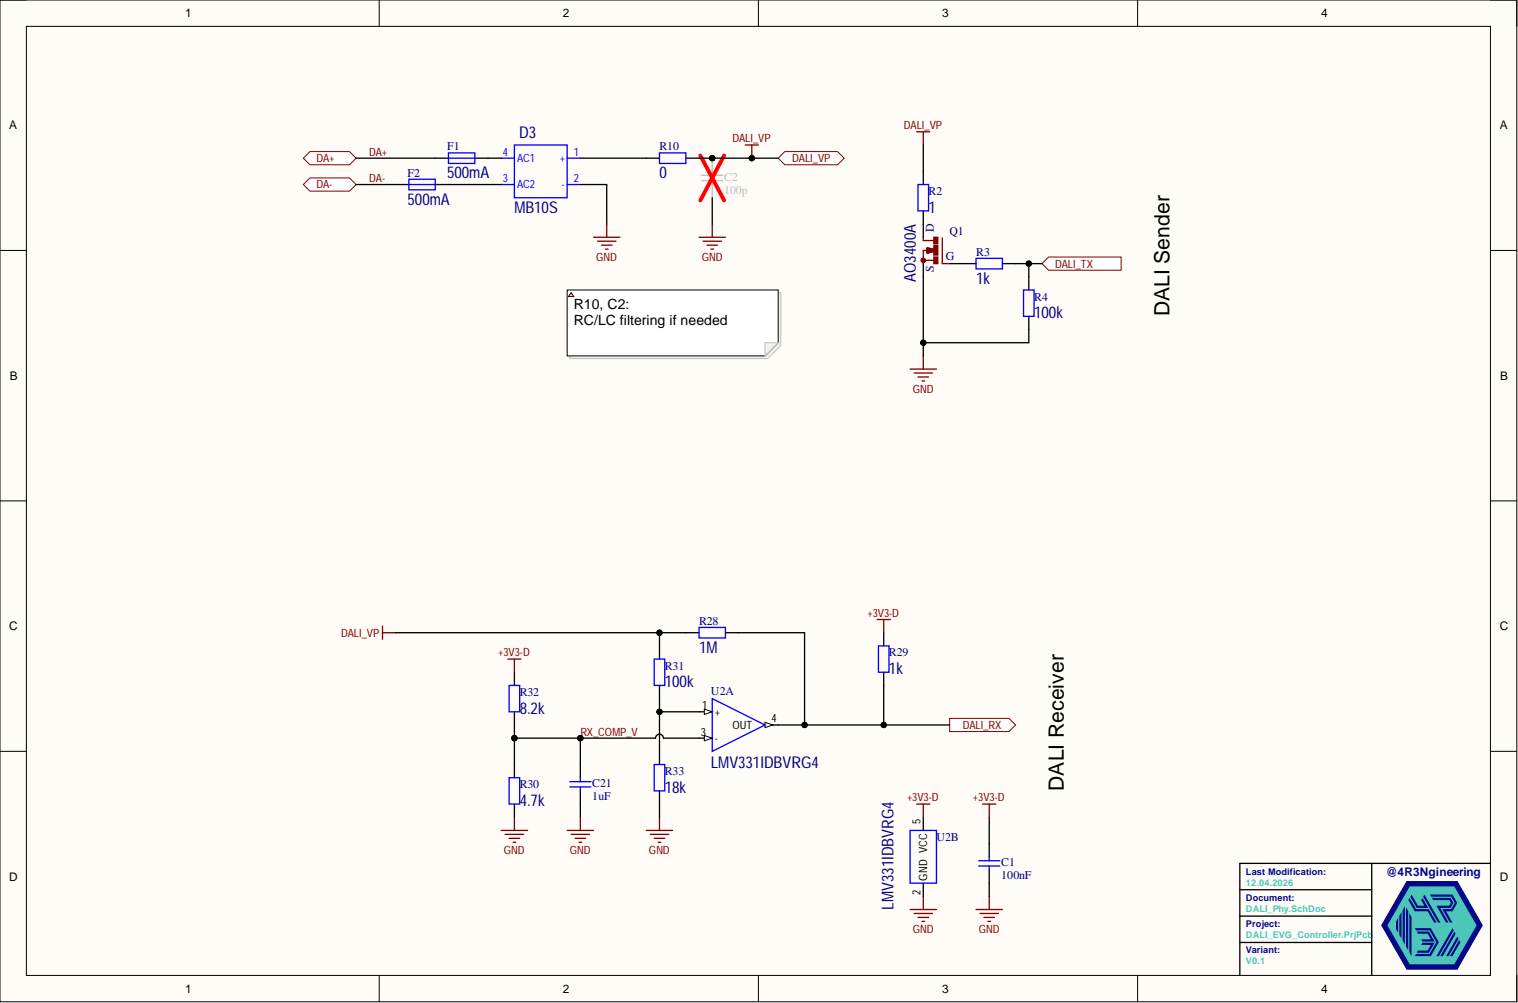
[picture p59: page 3]

RC/LC filtering if needed

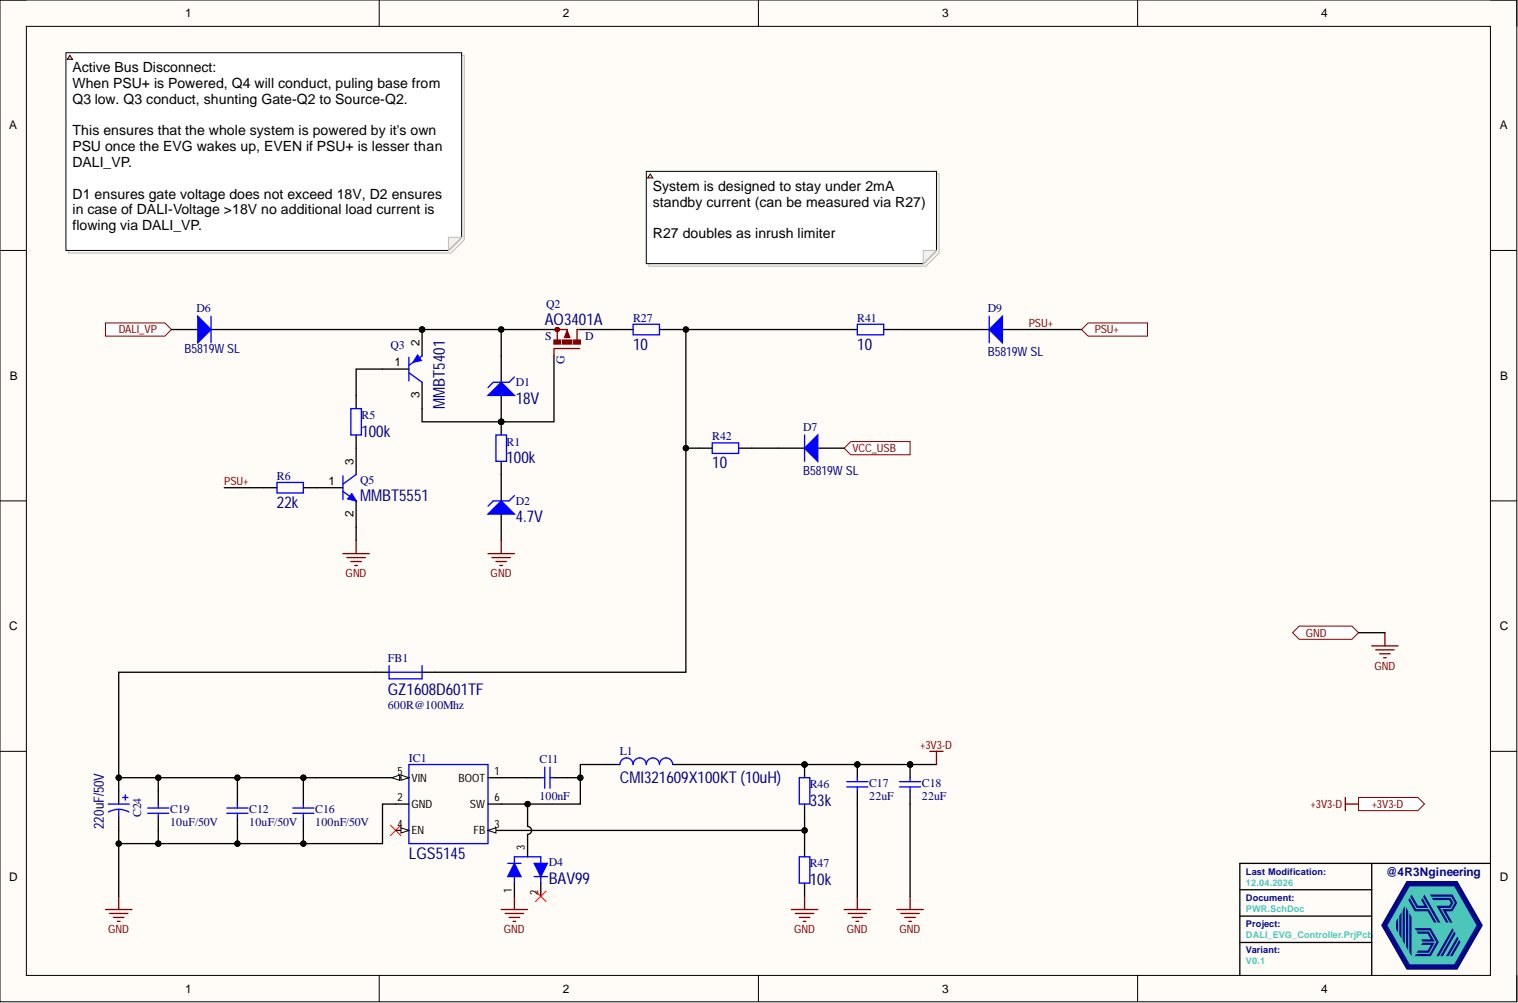
[picture p60: page 4]

Active Bus Disconnect:
When PSU+ is Powered, Q4 will conduct, puling base from
Q3 low. Q3 conduct, shunting Gate-Q2 to Source-Q2.

This ensures that the whole system is powered by it's own
PSU once the EVG wakes up, EVEN if PSU+ is lesser than
DALI_VP.

System is designed to stay under 2mA
standby current (can be measured via R27)

D1 ensures gate voltage does not exceed 18V, D2 ensures
in case of DALI-Voltage >18V no additional load current is
flowing via DALI_VP.

R27 doubles as inrush limiter
