cad435/OpenDALI_EVG/Hardware/Controller/DALI_EVG_Controller_V0.2-Pinout.PDF

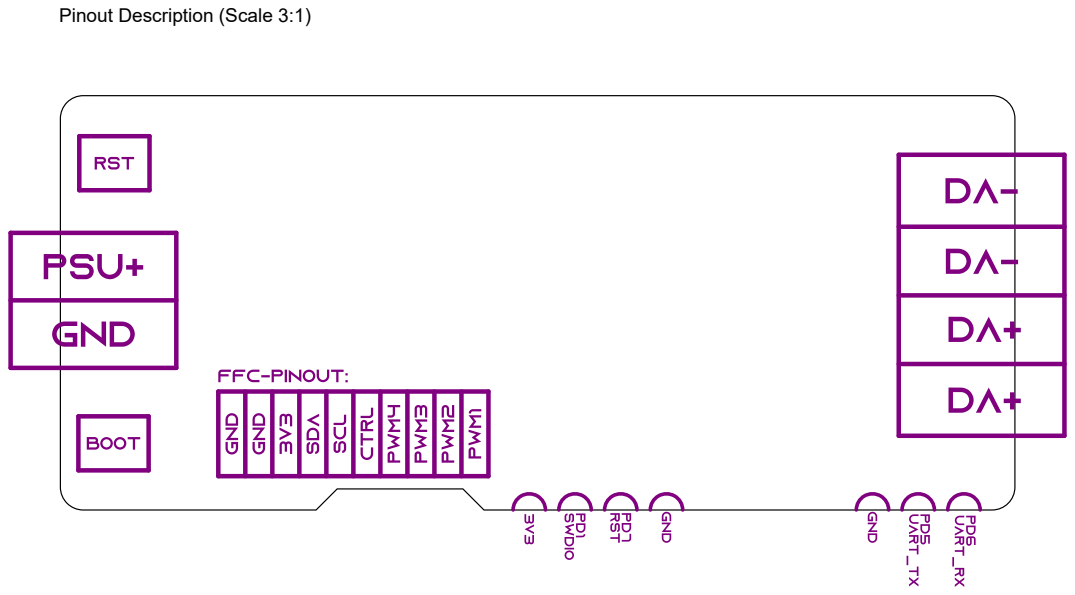
[picture p61: page 1]

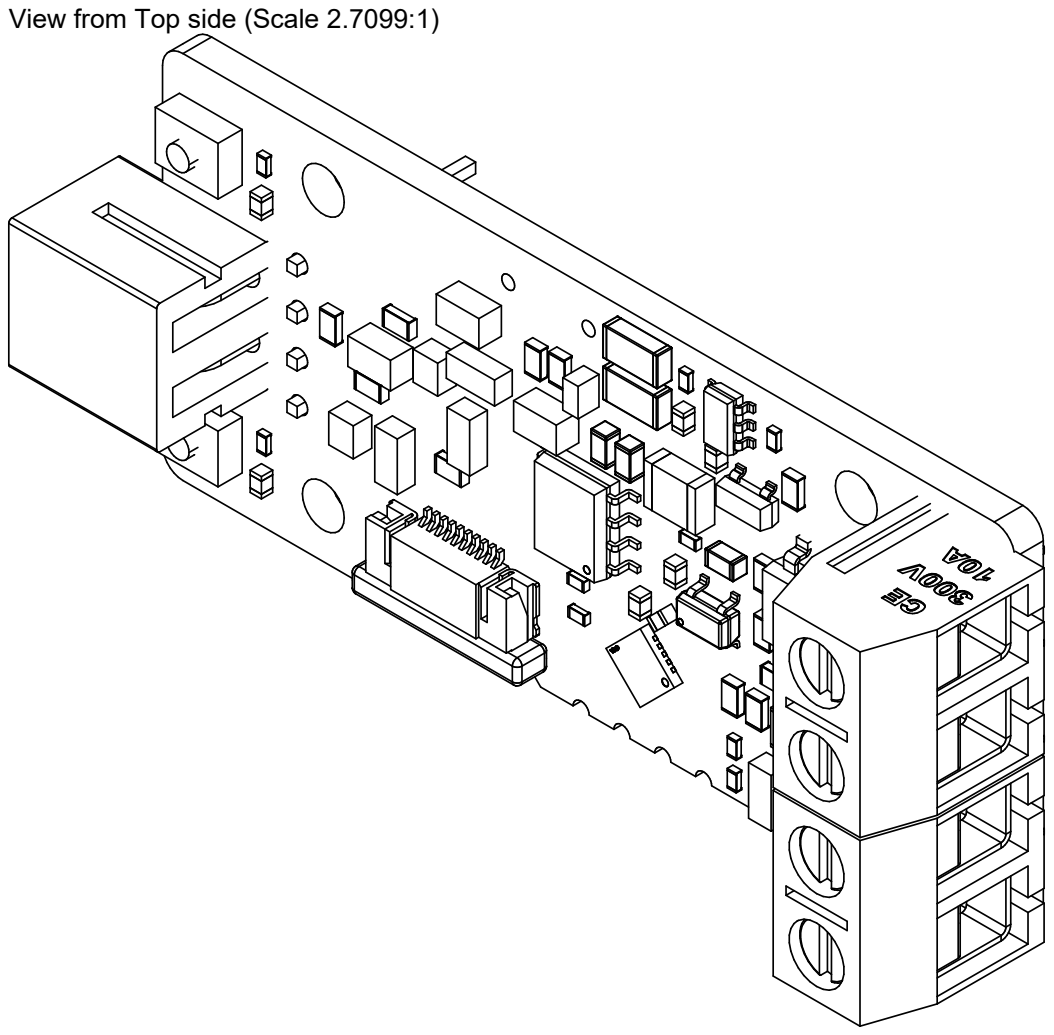
[picture p62: page 2]

View from Top side (Scale 2.7099:1)
