cad435/OpenDALI_EVG/Hardware/Controller/DALI_EVG_Controller_V0.1-Pinout.PDF

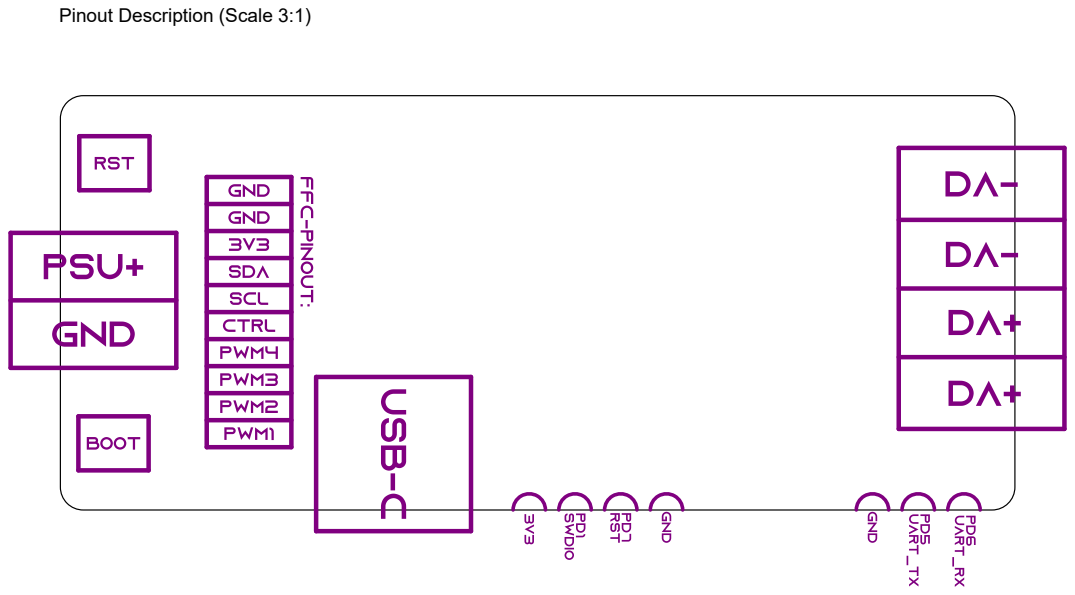
[picture p63: page 1]

Pinout Description (Scale 3:1)

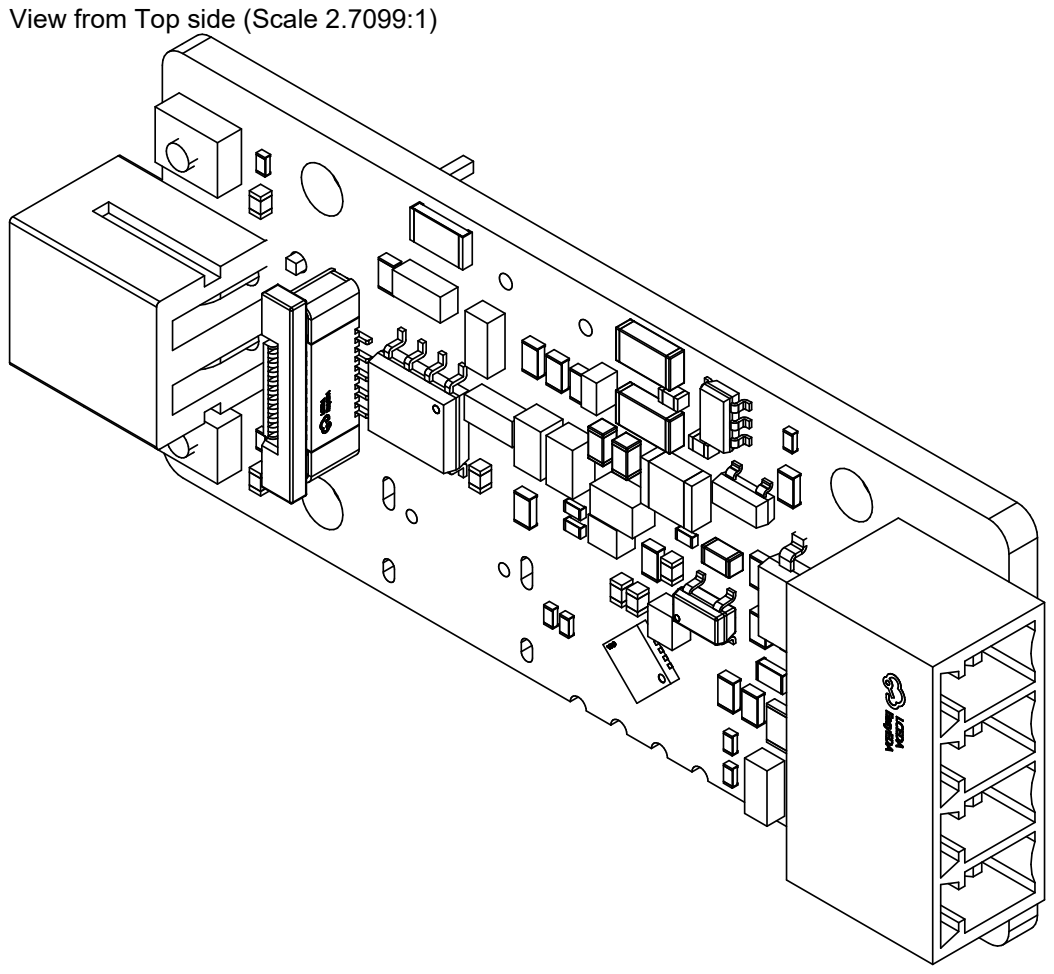
[picture p64: page 2]

View from Top side (Scale 2.7099:1)
