cad435/OpenDALI_EVG/Simulations/BusVoltage_Cutoff.asc

D1: zener; UMZ18K
D2: diode
D3: zener; 1N750
D4: diode
I1: current; 2m
M1: pmos; FDR840P
Q1: pnp; 2N2907
Q2: npn; 2N2222
R1: res; 100k
R2: res; 22k
R3: res; 100k
V1: voltage; 19
V2: voltage; PWL(0 0 100m 0 101m 5 200m 48)
Named nets: 0
Load
.tran 200m
Bus-Voltage
Secondary
Voltage
