cad435/OpenDALI_EVG/Simulations/Phy_Non-Isolated.asc

C2: cap; 1µ
C3: cap; 100µ
D1: diode; 1N4148
D2: diode; 1N4148
D9: diode
D11: diode
D12: diode
M1: nmos; AO6408
Q3: npn; 2N2222
R1: res; 2.3
R2: res; 1k
R4: res; 1
R6: res; 18k
R7: res; 100
R8: res; 10
R9: res; 825
R10: res; 1k
R11: res; 100k
R12: res; 8.2k
R13: res; 1k
R14: res; 1Meg
R15: res; 4.7k
U1: IDEAL_DCDC; Vout=3.3 Eff=0.85 Uvlo=6 Iq=45u
U3: LT1017
V1: voltage; 16
V2: voltage; PULSE(0 3.3 10m 1f 1f 0.4m 0.8m 16)
V6: voltage; PULSE(0 3.3 34.8m 1f 1f 0.4m 0.8m 16)
Named nets: 0, TX, DALI+, RX, 3.3V
.tran 60m
LGS5145
U3 = LMV331IDBVRG4
<-- MCU Current Draw!
Forward-Frame & Backward-Frame
DALI PSU
Selfpowered Supply
DALI Transmit (Backward Frames)
DALI Receive (Forward Frames)
