cad435/OpenDALI_EVG/Simulations/230V FET Switch.asc

C1: cap; 220n
C2: cap; 220n
D1: diode
D2: zener; BZX84C18VLY
D4: diode
D5: zener; BZX84C18VLY
M1: nmos; STP8NM60
M3: nmos; STP8NM60
R1: res; 100k
R2: res; 80k
R3: res; 100
R4: res; 100k
R5: res; 80k
R10: res; 200
U3: MOC3063
U4: MOC3063
V1: voltage; SINE(0 325 50)
V2: voltage; PULSE(0 3.3 4m 100u 100u 500m 1)
Named nets: 0, AC_OUT_N, AC_OUT_L, AC_IN_L, AC_IN_N
.tran 2
.options maxstep=10u method=gear
