cad435/OpenDALI_EVG/Simulations/Sec_Linear_Regulator.asc

C1: cap; 10µ
D1: zener; BZX84B6V8L
I1: current; PULSE(0 10m 0 1f 1f 25u 50u)
Q1: npn; 2N5550
R1: res; 22k
R2: res; 100k
V1: voltage; 24
Named nets: 0
.tran 10m
