cad435/OpenDALI_EVG/Simulations/Phy_Isolated.asc

C2: cap; 1µ
C3: cap; 100µ
C4: cap; 10µ
C5: cap; 10µ
D1: diode; 1N4148
D2: diode; 1N4148
D3: diode
D9: diode
D10: diode
D11: diode
D12: diode
Q3: npn; 2N2222
Q4: pnp; 2N3906
Q5: npn; 2N2222
R1: res; 2.3
R2: res; 120
R3: res; 1k
R4: res; 10
R5: res; 330k
R6: res; 240k
R7: res; 1k
R8: res; 100
R9: res; 825
R10: res; 1k
R11: res; 15k
R12: res; 1
R13: res; 1k
R14: res; 1.5Meg
R15: res; 10k
R16: res; 1
U1: IDEAL_DCDC; Vout=3.3 Eff=0.85 Uvlo=6 Iq=45u
U2: PC817C
U3: LT1017
U4: PC817D
V1: voltage; 17
V2: voltage; PULSE(0 3.3 10m 1f 1f 0.4m 0.8m 16)
V6: voltage; PULSE(0 3.3 34.8m 1f 1f 0.4m 0.8m 16)
Named nets: 0, TX, DALI+, DALI-, RX, RX_SUP, 3.3V
.tran 20m
TPS54202
LTV-217-B-G
LTV-217-B-G
U3 = RUNIC LM331CXF (NOT TI!)
<-- MCU Current Draw!
Forward-Frame & Backward-Frame
DALI PSU
Selfpowered Supply
DALI Transmit (Backward Frames)
DALI Receive Forward Frames)
